CircuitGuy943/ESP32-S3-TFT-Display-Devboard/Pictures/IMG_20260306_161905.jpg

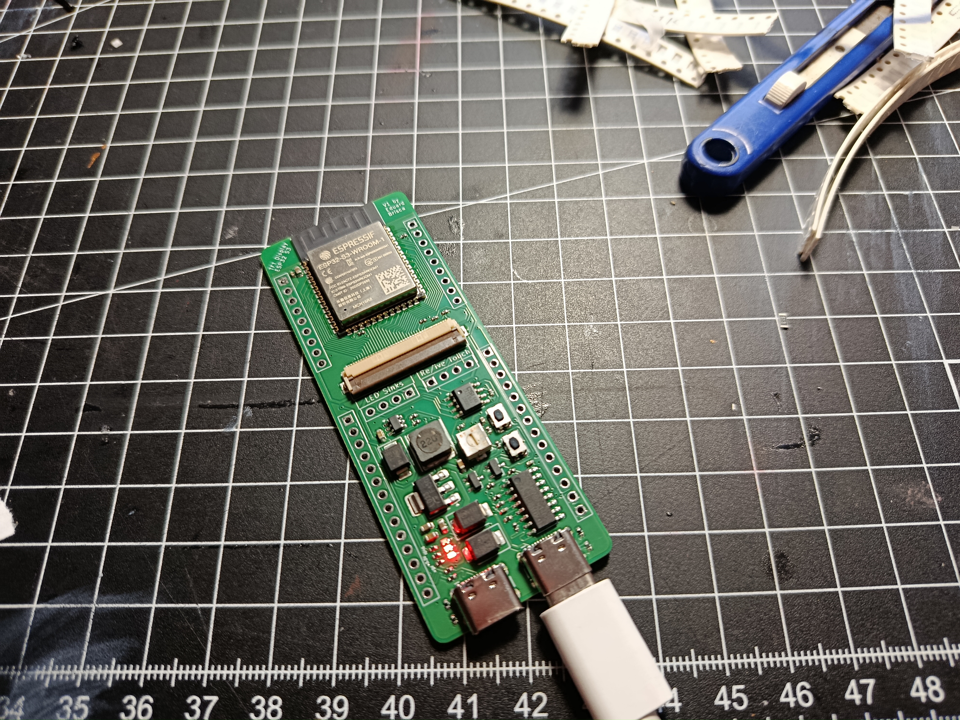
Pictures/IMG_20260306_161905.jpg
