CircuitGuy943/ESP32-S3-TFT-Display-Devboard/Pictures/IMG_20260306_164611.jpg

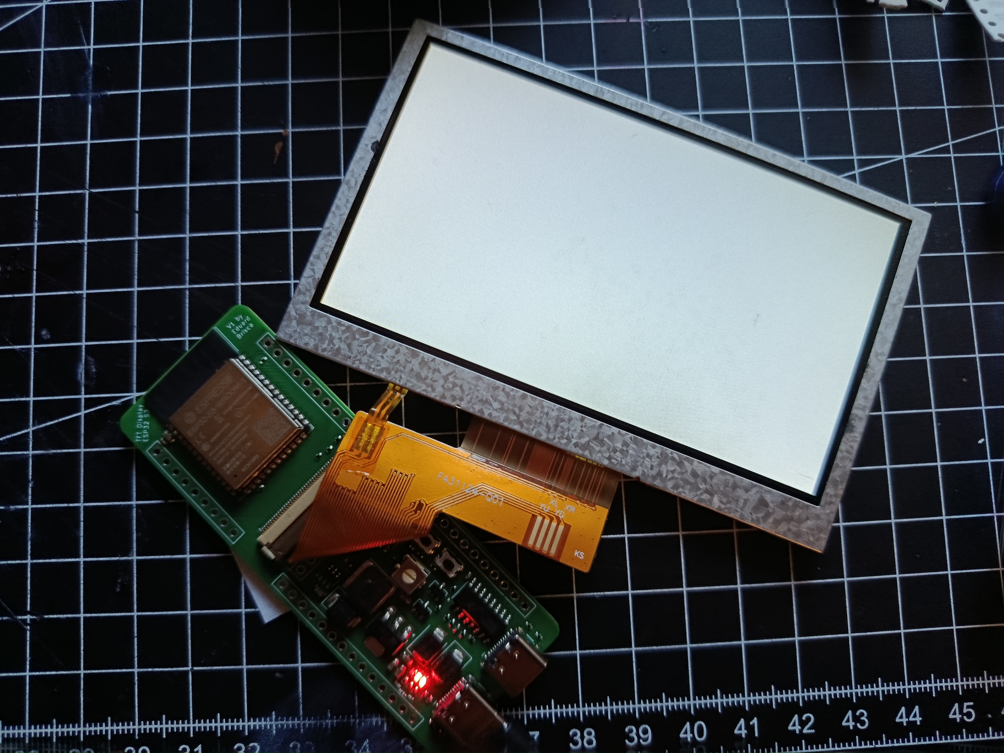
Pictures/IMG_20260306_164611.jpg
