CircuitGuy943/ESP32-S3-TFT-Display-Devboard/Pictures/IMG_20260308_182814.jpg

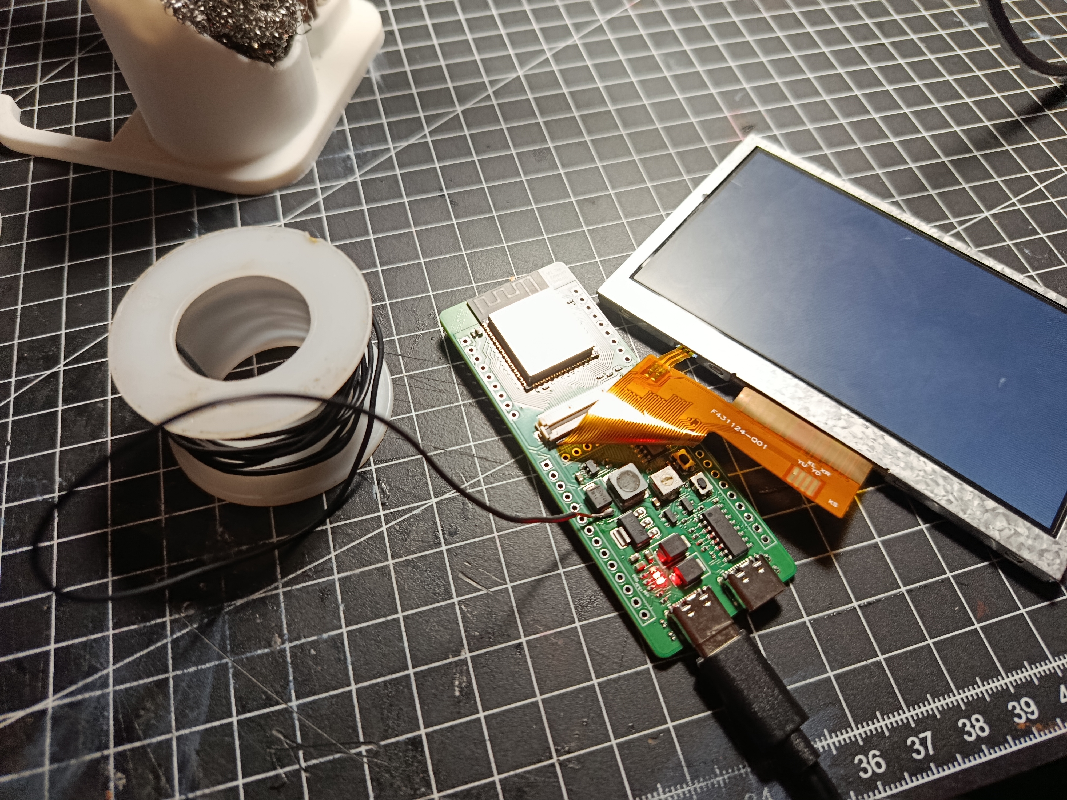
Pictures/IMG_20260308_182814.jpg
